stolau/AlarmClock/Version 2/Pictures/AlarmClockV1.png

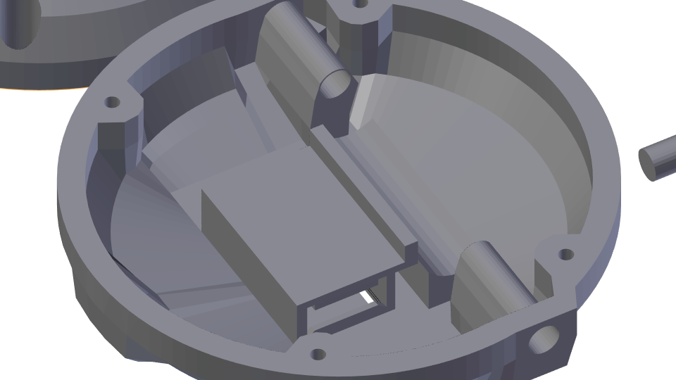
Version 2/Pictures/AlarmClockV1.png
