stolau/AlarmClock/Version 2/Pictures/AlarmClockV1pic1.png

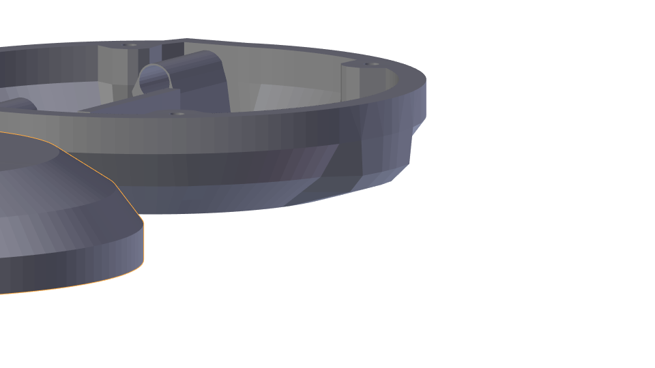
Version 2/Pictures/AlarmClockV1pic1.png
