stolau/AlarmClock/Version 2/Pictures/AlarmClockV1pic2.png

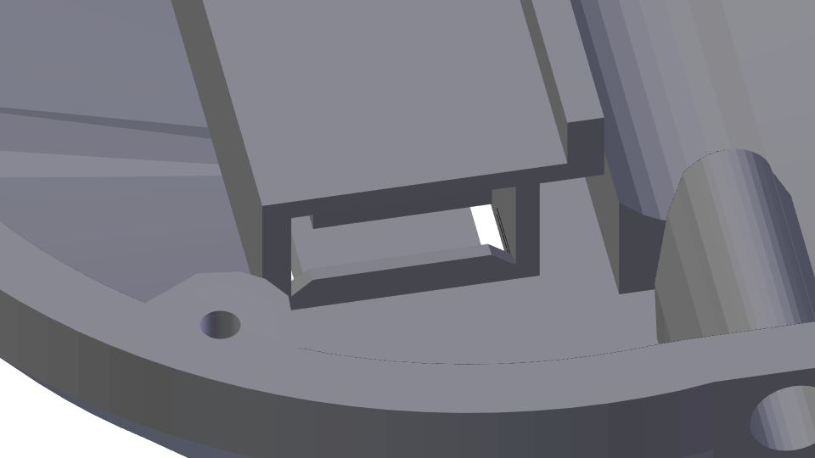
Version 2/Pictures/AlarmClockV1pic2.png
