stolau/AlarmClock/Version 2/Pictures/AlarmClockV1pic3.png

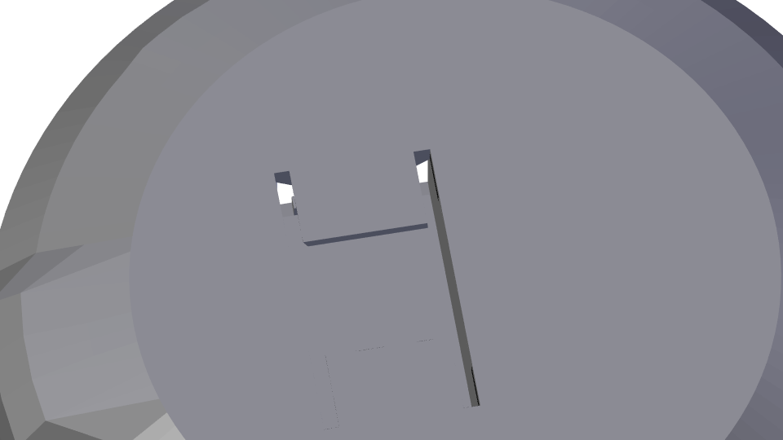
Version 2/Pictures/AlarmClockV1pic3.png
