stolau/AlarmClock/Version 2/Pictures/AlarmClockV1pic4.png

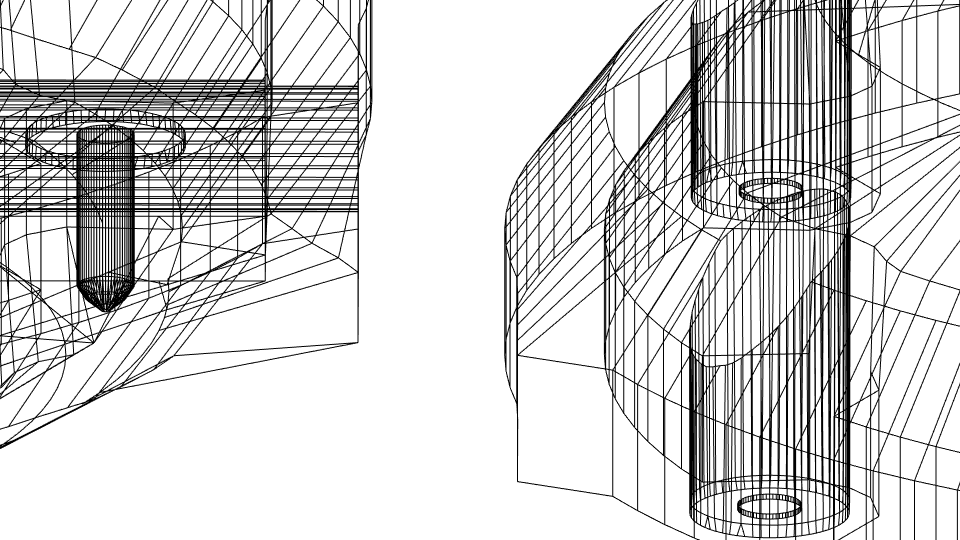
Version 2/Pictures/AlarmClockV1pic4.png
