stolau/AlarmClock/Version 2/Pictures/AlarmClockV2BatteryContainer1.png

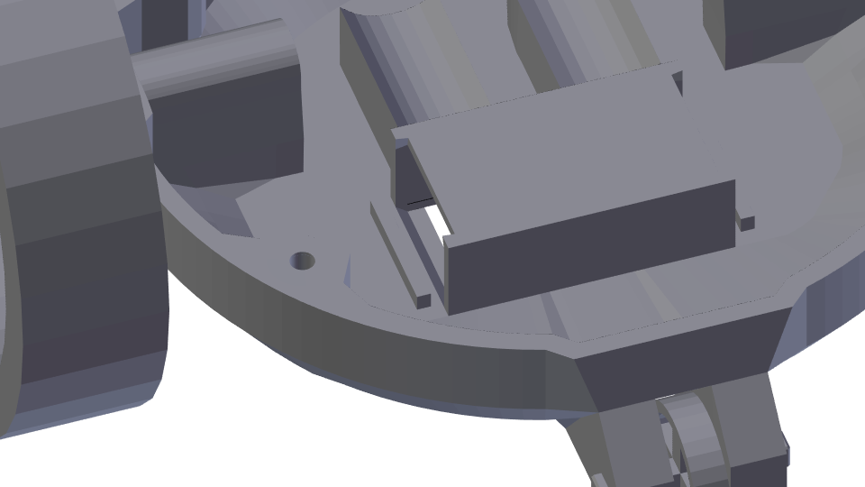
Version 2/Pictures/AlarmClockV2BatteryContainer1.png
