stolau/AlarmClock/Version 2/Pictures/AlarmClockV2BatteryContainer2.png

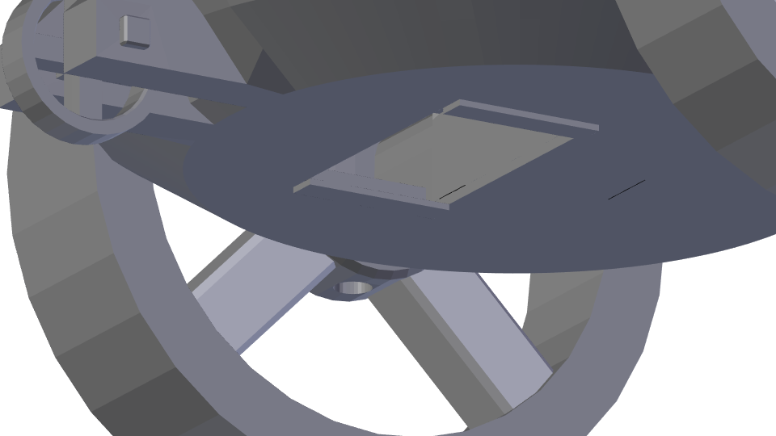
Version 2/Pictures/AlarmClockV2BatteryContainer2.png
