stolau/AlarmClock/Version 2/Pictures/AlarmClockV2Front.png

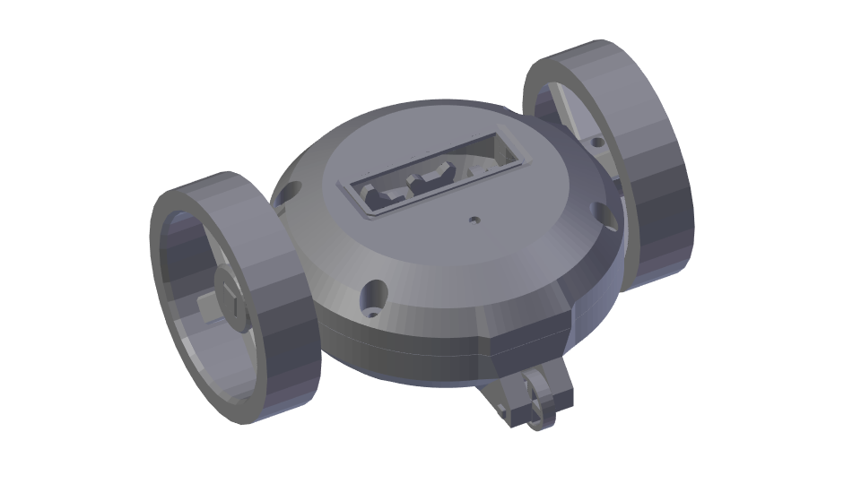
Version 2/Pictures/AlarmClockV2Front.png
