stolau/AlarmClock/Version 2/Pictures/AlarmClockV2FrontWheel.png

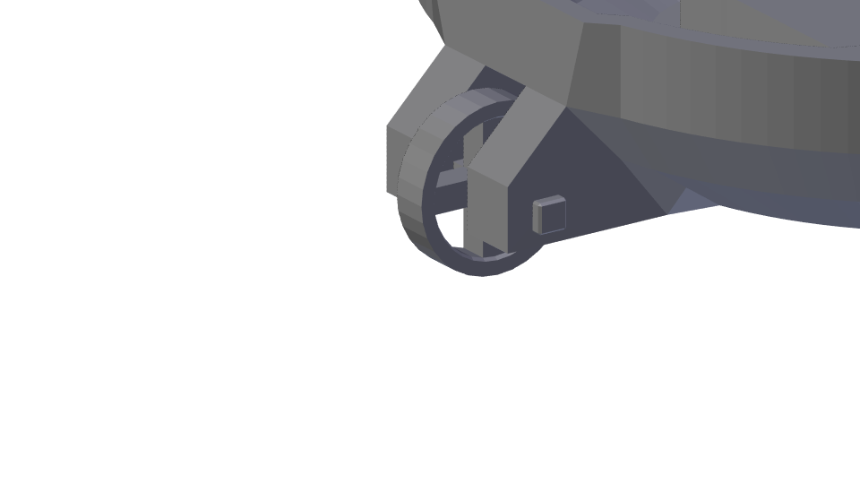
Version 2/Pictures/AlarmClockV2FrontWheel.png
