stolau/AlarmClock/Version 2/Pictures/AlarmClockV2Holder.png

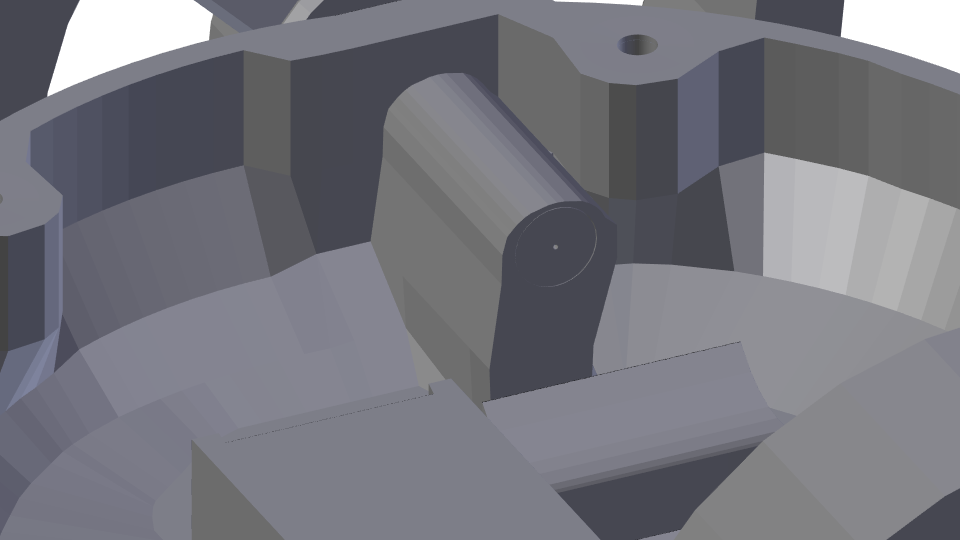
Version 2/Pictures/AlarmClockV2Holder.png
