stolau/AlarmClock/Version 2/Pictures/AlarmClockV2Inside.png

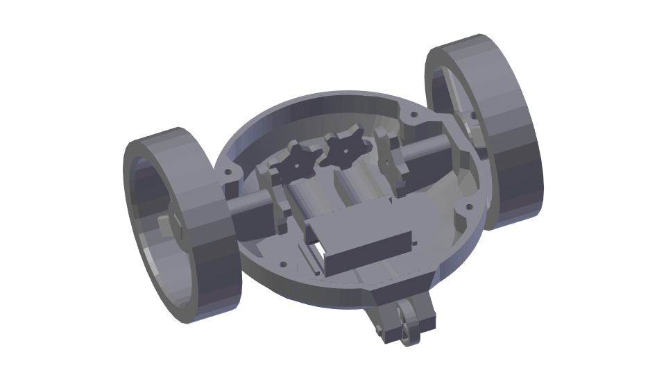
Version 2/Pictures/AlarmClockV2Inside.png
