stolau/AlarmClock/Version 2/Pictures/AlarmClockV2InsidesMadeThiner2.png

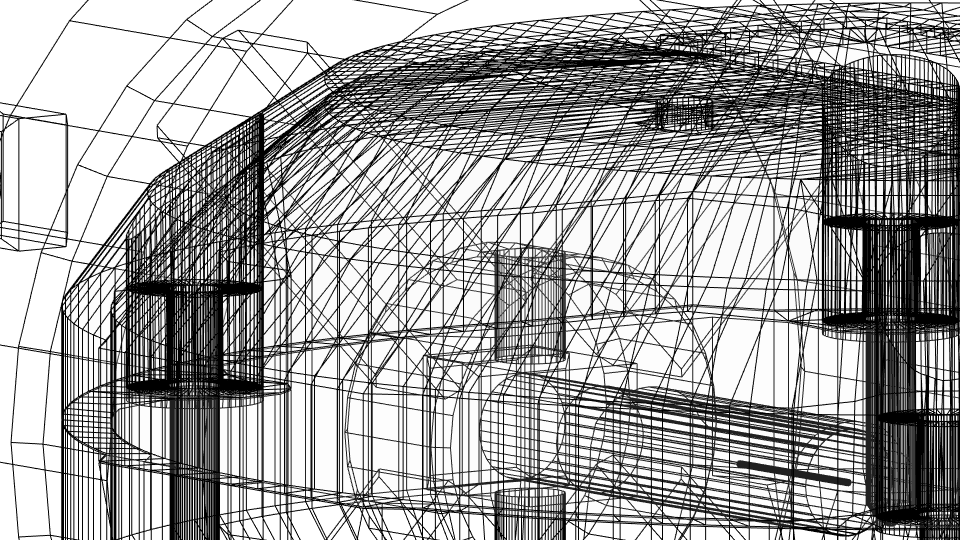
Version 2/Pictures/AlarmClockV2InsidesMadeThiner2.png
