stolau/AlarmClock/Version 2/Pictures/AlarmClockV2InsidesMadeThiner.png

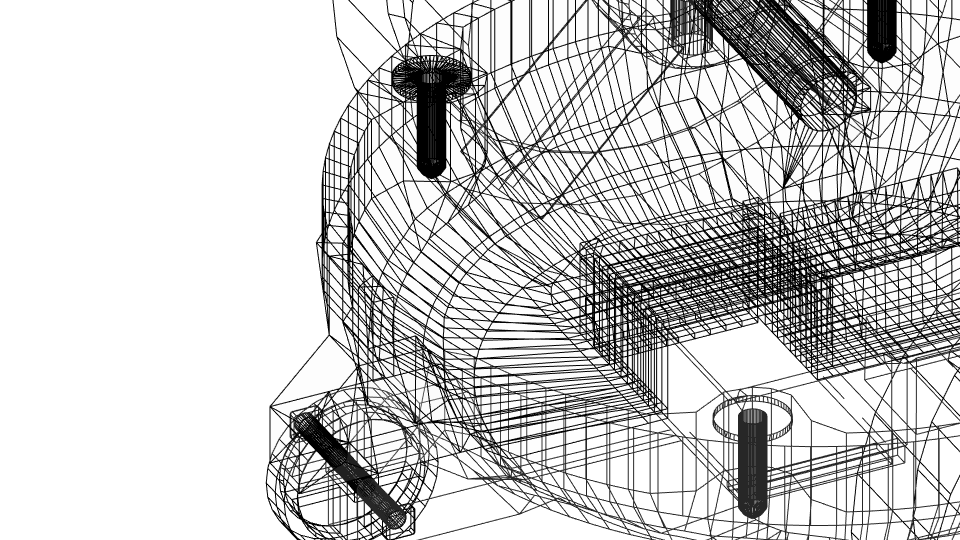
Version 2/Pictures/AlarmClockV2InsidesMadeThiner.png
