stolau/AlarmClock/Version 2/Pictures/AlarmClockV2ScrewHolder.png

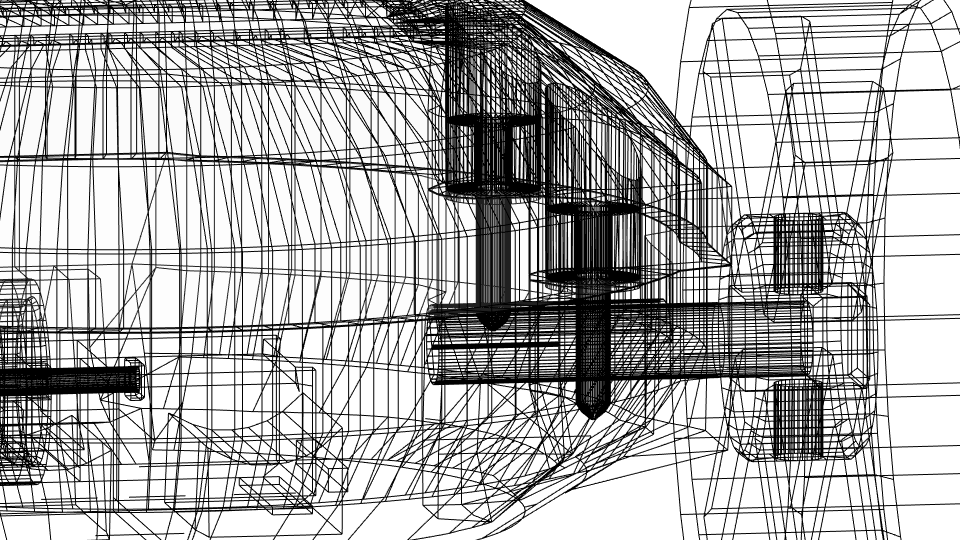
Version 2/Pictures/AlarmClockV2ScrewHolder.png
