stolau/AlarmClock/Week 1 Report/Initial_sketches_of_model/AlarmClockSketch.jpeg

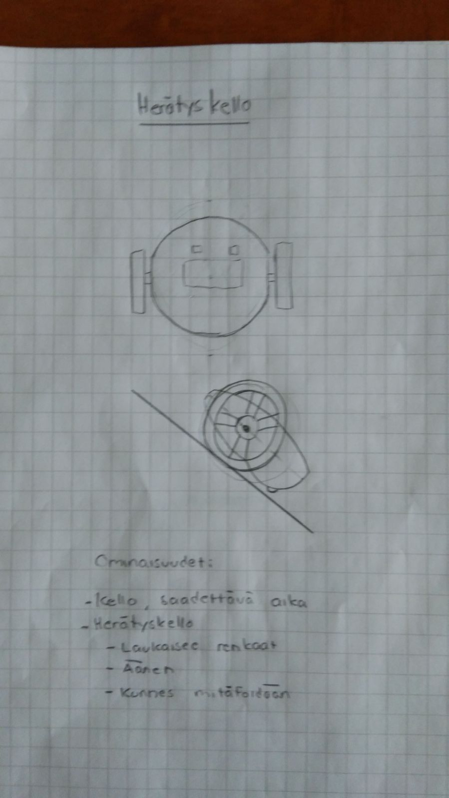
Week 1 Report/Initial_sketches_of_model/AlarmClockSketch.jpeg
