stolau/AlarmClock/Week 1 Report/Initial_sketches_of_model/AlarmClockSketch_01.jpeg

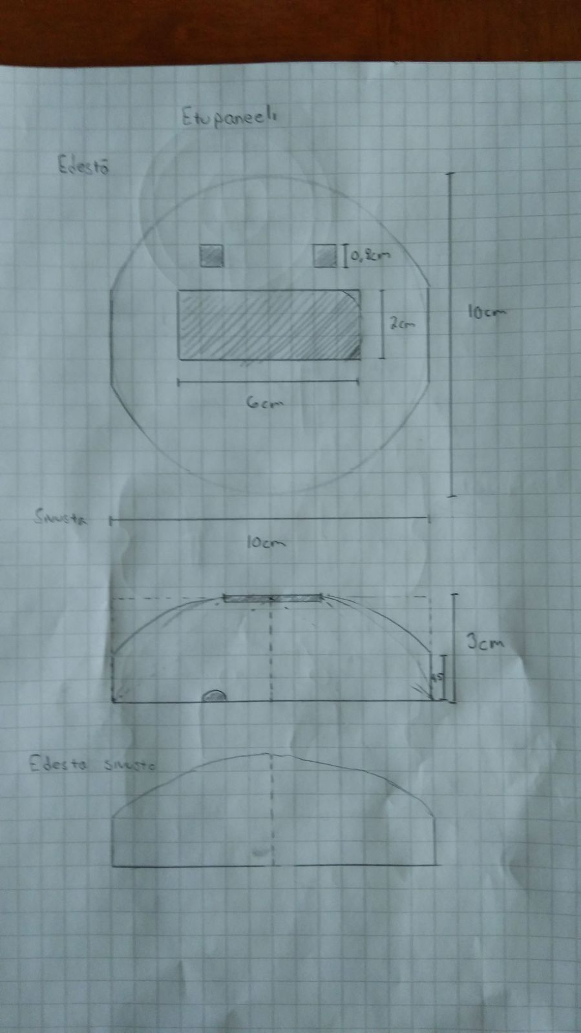
Week 1 Report/Initial_sketches_of_model/AlarmClockSketch_01.jpeg
