stolau/AlarmClock/Week 6 Report/circuitdiagram.jpeg

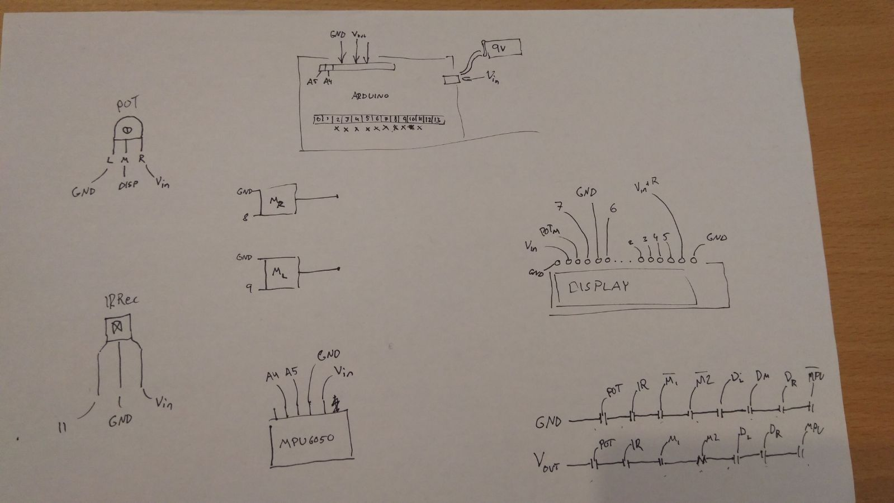
Week 6 Report/circuitdiagram.jpeg
