stolau/AlarmClock/Week 6 Report/pic2.jpeg

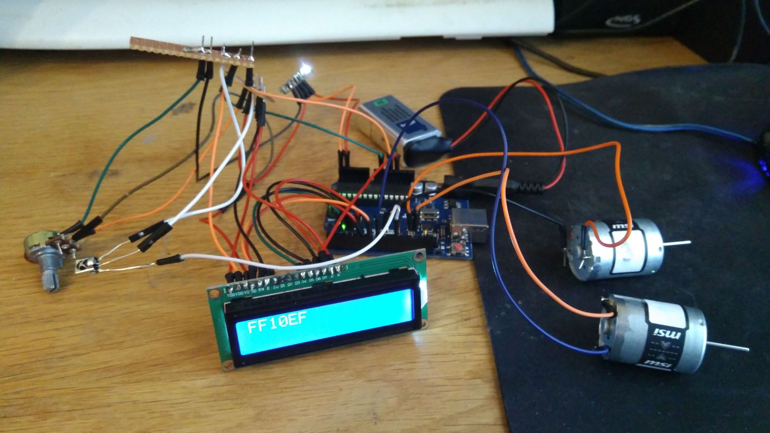
Week 6 Report/pic2.jpeg
